opieters/MIRRA/3d_printing/radiation_shield/radiation_shield.scad

include <radiation_shield_optimised.scad>
include <radiation_shield_internal.scad>
include <hook.scad>

shield();
