opieters/MIRRA/firmware/sensor_node/sensornode.cpp

#include "sensornode.h"

#include <BatterySensor.h>
#include <ESPCamUART.h>
#include <LightSensor.h>
#include <RandomSensor.h>
#include <SoilTempSensor.h>
#include <TempHumiSensor.h>

RTC_DATA_ATTR bool initialBoot = true;

RTC_DATA_ATTR std::array<uint32_t, MAX_SENSORS> sensorsNextSampleTimes{0};
RTC_DATA_ATTR uint32_t sampleInterval{DEFAULT_SAMPLING_INTERVAL};
RTC_DATA_ATTR uint32_t sampleRounding{DEFAULT_SAMPLING_ROUNDING};
RTC_DATA_ATTR uint32_t sampleOffset{DEFAULT_SAMPLING_OFFSET};
RTC_DATA_ATTR uint32_t nextSampleTime = -1;
RTC_DATA_ATTR uint32_t commInterval;
RTC_DATA_ATTR uint32_t nextCommTime = -1;
RTC_DATA_ATTR uint32_t maxMessages;
RTC_DATA_ATTR MACAddress gatewayMAC;

SensorNode::SensorNode(const MIRRAPins& pins) : MIRRAModule(pins)
{
    if (initialBoot)
    {
        if (!LittleFS.exists(DATA_FP))
        {
            File dataFile{LittleFS.open(DATA_FP, FILE_WRITE, true)};
            dataFile.close();
        }
        initSensors();
        clearSensors();
        discovery();
        initialBoot = false;
    }
}

void SensorNode::wake()
{
    Log::debug("Running wake()...");
    uint32_t cTime{rtc.getSysTime()};
    if (cTime >= WAKE_COMM_PERIOD(nextCommTime))
        commPeriod();
    cTime = rtc.getSysTime();
    if (cTime >= nextSampleTime)
    {
        samplePeriod();
    }
    cTime = rtc.getSysTime();
    Log::info("Next sample in ", nextSampleTime - cTime, "s, next comm period in ", nextCommTime - cTime, "s");
    Serial.printf("Welcome! This is Sensor Node %s\n", lora.getMACAddress().toString());
    commandEntry.prompt(Commands(this));
    cTime = rtc.getSysTime();
    if (cTime >= nextCommTime || cTime >= nextSampleTime)
        wake();
    Log::debug("Entering deep sleep...");
    deepSleepUntil(std::min(WAKE_COMM_PERIOD(nextCommTime), nextSampleTime));
}

void SensorNode::discovery()
{
    Log::info("Awaiting discovery message...");
    auto hello = lora.receiveMessage<HELLO>(DISCOVERY_TIMEOUT);
    if (!hello)
    {
        Log::error("Error while awaiting discovery message from gateway. Aborting discovery listening.");
        return;
    }
    const MACAddress& gatewayMAC = hello->getSource();
    Log::info("Gateway found at ", gatewayMAC.toString(), ". Sending response message...");
    lora.sendMessage(Message<HELLO_REPLY>(lora.getMACAddress(), gatewayMAC));
    Log::debug("Awaiting time config message...");
    auto timeConfig = lora.receiveMessage<TIME_CONFIG>(TIME_CONFIG_TIMEOUT, TIME_CONFIG_ATTEMPTS, gatewayMAC);
    if (!timeConfig)
    {
        Log::error("Error while awaiting time config message from gateway. Aborting discovery listening.");
        return;
    }
    this->timeConfig(*timeConfig);
    Log::debug("Time config message received. Sending TIME_ACK");
    lora.sendMessage(Message<ACK_TIME>(lora.getMACAddress(), gatewayMAC));
    lora.receiveMessage<REPEAT>(TIME_CONFIG_TIMEOUT, 0, gatewayMAC);
}

void SensorNode::timeConfig(Message<TIME_CONFIG>& m)
{
    rtc.writeTime(m.getCTime());
    rtc.setSysTime();
    bool scheduleValid{sampleInterval == m.getSampleInterval() && sampleRounding == m.getSampleRounding() && sampleOffset == m.getSampleOffset()};
    sampleInterval = m.getSampleInterval() == 0 ? DEFAULT_SAMPLING_INTERVAL : m.getSampleInterval();
    sampleRounding = m.getSampleRounding() == 0 ? DEFAULT_SAMPLING_ROUNDING : m.getSampleRounding();
    sampleOffset = m.getSampleOffset();
    commInterval = m.getCommInterval();
    nextCommTime = m.getCommTime();
    maxMessages = m.getMaxMessages();
    gatewayMAC = m.getSource();
    if (!scheduleValid)
    {
        sensorsNextSampleTimes.fill(0);
        initSensors();
        clearSensors();
    }
    Log::info("Sample interval: ", sampleInterval, ", Comm interval: ", commInterval, ", Max messages: ", maxMessages,
              ", Gateway MAC: ", gatewayMAC.toString());
}

void SensorNode::addSensor(std::unique_ptr<Sensor>&& sensor)
{
    if (nSensors > MAX_SENSORS)
        return;
    uint32_t cTime{rtc.getSysTime()};
    if (sensorsNextSampleTimes[nSensors] == 0)
    {
        sensor->setNextSampleTime(((cTime / sampleRounding) * sampleRounding + sampleOffset));
        while (sensor->getNextSampleTime() <= cTime)
            sensor->updateNextSampleTime(sampleInterval);
    }
    else
    {
        sensor->setNextSampleTime(sensorsNextSampleTimes[nSensors]);
    }
    sensor->setup();
    sensors[nSensors] = std::move(sensor);
    nSensors++;
}

void SensorNode::initSensors()
{
    addSensor(std::make_unique<RandomSensor>(rtc.getSysTime()));
    addSensor(std::make_unique<SoilTemperatureSensor>(SOILTEMP_PIN, SOILTEMP_BUS_INDEX));
    addSensor(std::make_unique<LightSensor>());
    addSensor(std::make_unique<TempSHTSensor>());
    addSensor(std::make_unique<HumiSHTSensor>(*reinterpret_cast<TempSHTSensor*>(sensors[nSensors - 1].get())));
    addSensor(std::make_unique<BatterySensor>(BATT_PIN, BATT_EN_PIN));
    addSensor(std::make_unique<ESPCamUART>(&Serial1, CAM_PIN));
}

void SensorNode::clearSensors()
{
    nextSampleTime = -1;
    for (size_t i{0}; i < nSensors; i++)
    {
        sensorsNextSampleTimes[i] = sensors[i]->getNextSampleTime();
        if (sensors[i]->getNextSampleTime() < nextSampleTime)
            nextSampleTime = sensors[i]->getNextSampleTime();
        sensors[i].reset();
    }
    nSensors = 0;
}

Message<SENSOR_DATA> SensorNode::sampleAll()
{
    Log::info("Sampling all sensors...");
    for (size_t i{0}; i < nSensors; i++)
    {
        Serial.printf("Starting measurement for %u\n", sensors[i]->getID());
        sensors[i]->startMeasurement();
    }
    std::array<SensorValue, Message<SENSOR_DATA>::maxNValues> values;
    for (size_t i{0}; i < nSensors; i++)
    {
        Serial.printf("Getting measurement for %u\n", sensors[i]->getID());
        values[i] = sensors[i]->getMeasurement();
    }
    return Message<SENSOR_DATA>(lora.getMACAddress(), gatewayMAC, 0, static_cast<uint8_t>(nSensors), values);
}

Message<SENSOR_DATA> SensorNode::sampleScheduled(uint32_t cTime)
{
    Log::info("Sampling scheduled sensors...");
    for (size_t i{0}; i < nSensors; i++)
    {
        if (sensors[i]->getNextSampleTime() == cTime)
            sensors[i]->startMeasurement();
    }
    std::array<SensorValue, Message<SENSOR_DATA>::maxNValues> values;
    uint8_t nValues{0};
    for (size_t i{0}; i < nSensors; i++)
    {
        if (sensors[i]->getNextSampleTime() == cTime)
        {
            values[nValues] = sensors[i]->getMeasurement();
            nValues++;
        }
    }
    return Message<SENSOR_DATA>(lora.getMACAddress(), gatewayMAC, cTime, nValues, values);
}

void SensorNode::updateSensorsSampleTimes(uint32_t cTime)
{
    for (size_t i = 0; i < nSensors; i++)
    {
        while (sensors[i]->getNextSampleTime() <= cTime)
            sensors[i]->updateNextSampleTime(sampleInterval);
    }
}
void SensorNode::samplePeriod()
{
    initSensors();
    auto lambdaByNextSampleTime = [](const std::unique_ptr<Sensor>& a, const std::unique_ptr<Sensor>& b)
    { return a->getNextSampleTime() < b->getNextSampleTime(); };
    uint32_t cTime{(*std::min_element(sensors.begin(), std::next(sensors.begin(), nSensors), lambdaByNextSampleTime))->getNextSampleTime()};
    Message<SENSOR_DATA> message{sampleScheduled(cTime)};
    Log::debug("Constructed Sensor Message with length ", message.getLength());
    File data = LittleFS.open(DATA_FP, FILE_APPEND);
    storeSensorData(message, data);
    data.close();
    updateSensorsSampleTimes(cTime);
    clearSensors();
}

void SensorNode::commPeriod()
{
    uint32_t cTime{rtc.getSysTime()};
    if (cTime >= nextCommTime + (SENSOR_DATA_TIMEOUT / 1000))
    {
        Log::error("Too late to start comm period. Skipping and assuming next comm period from given interval.");
        while (nextCommTime <= cTime)
            nextCommTime += commInterval;
        return;
    }
    MACAddress _gatewayMAC{gatewayMAC}; // avoid access to slow RTC memory
    Log::info("Communicating with gateway ", _gatewayMAC.toString(), " ...");
    uint32_t _maxMessages{maxMessages}; // avoid access to slow RTC memory
    Log::debug("Max messages to send: ", _maxMessages);
    std::vector<Message<SENSOR_DATA>> messages;
    messages.reserve(_maxMessages);
    uint32_t messagesFlagPositions[_maxMessages];
    File dataFile = LittleFS.open(DATA_FP, "r+");
    while (dataFile.available())
    {
        if (messages.size() == _maxMessages)
            break;
        uint8_t size{static_cast<uint8_t>(dataFile.read())};
        uint8_t buffer[size];
        dataFile.read(buffer, size);
        if (buffer[0] == 0) // not yet uploaded
        {
            messagesFlagPositions[messages.size()] = dataFile.position() - size;
            Log::debug("Reconstructing message from buffer...");
            Message<SENSOR_DATA>& message{Message<SENSOR_DATA>::fromData(buffer)};
            message.setType(SENSOR_DATA);
            if ((messages.size() == _maxMessages - 1) ||
                (!dataFile.available())) // imperfect: assumes the last message in the data file is always one that has not been uploaded yet
            {
                Log::debug("Last sensor data message...");
                message.setLast();
            }
            messages.push_back(message);
        }
    }
    bool uploadSuccess[messages.size()];
    bool firstMessage{true};
    for (size_t i{0}; i < messages.size(); i++)
        uploadSuccess[i] = sendSensorMessage(messages[i], _gatewayMAC, firstMessage);
    for (size_t i{0}; i < messages.size(); i++)
    {
        if (uploadSuccess[i])
        {
            dataFile.seek(messagesFlagPositions[i]);
            dataFile.write(1);
        }
    }
    Log::debug("Messages that were uploaded have been marked as such.");
    dataFile.seek(0);
    pruneSensorData(std::move(dataFile), MAX_SENSORDATA_FILESIZE);
}

bool SensorNode::sendSensorMessage(Message<SENSOR_DATA>& message, MACAddress const& dest, bool& firstMessage)
{
    Log::debug("Sending data message...");
    if (firstMessage)
    {
        lightSleepUntil(nextCommTime);
        lora.sendMessage(message, 0); // gateway should already be listening for first message
        firstMessage = false;
    }
    else
    {
        lora.sendMessage(message);
    }
    Log::debug("Awaiting acknowledgement...");
    if (!message.isLast())
    {
        auto dataAck{lora.receiveMessage<ACK_DATA>(SENSOR_DATA_TIMEOUT, SENSOR_DATA_ATTEMPTS, dest)};
        if (dataAck)
        {
            return 1;
        }
        else
        {
            Log::error("Error while uploading to gateway.");
            return 0;
        }
    }
    else
    {
        auto timeConfig{lora.receiveMessage<TIME_CONFIG>(TIME_CONFIG_TIMEOUT, TIME_CONFIG_ATTEMPTS, dest)};
        if (timeConfig)
        {
            this->timeConfig(*timeConfig);
            lora.sendMessage(Message<ACK_TIME>(lora.getMACAddress(), dest));
            lora.receiveMessage<REPEAT>(TIME_CONFIG_TIMEOUT, 0, gatewayMAC);
            return 1;
        }
        else
        {
            Log::error("Error while receiving new time config from gateway. Assuming next comm period from given interval.");
            while (nextCommTime <= rtc.getSysTime())
                nextCommTime += commInterval;
            return 0;
        }
    }
}

CommandCode SensorNode::Commands::discovery()
{
    parent->discovery();
    return COMMAND_SUCCESS;
}
CommandCode SensorNode::Commands::sample()
{
    parent->samplePeriod();
    return COMMAND_SUCCESS;
}

CommandCode SensorNode::Commands::printSample()
{
    parent->initSensors();
    Message<SENSOR_DATA> message{parent->sampleAll()};
    auto& values = message.getValues();
    Serial.println("TAG\tVALUE");
    for (size_t i{0}, nValues{message.getNValues()}; i < nValues; i++)
    {
        Serial.printf("%u\t%f\n", values[i].tag, values[i].value);
    }
    parent->clearSensors();
    return COMMAND_SUCCESS;
}

CommandCode SensorNode::Commands::printSchedule()
{
    parent->initSensors();
    constexpr size_t timeLength{sizeof("0000-00-00 00:00:00")};
    char buffer[timeLength]{0};
    Serial.println("TAG\tNEXT SAMPLE");
    for (size_t i{0}; i < parent->nSensors; i++)
    {
        tm time;
        time_t nextSensorSampleTime{static_cast<time_t>(parent->sensors[i]->getNextSampleTime())};
        gmtime_r(&nextSensorSampleTime, &time);
        strftime(buffer, timeLength, "%F %T", &time);
        Serial.printf("%u\t%s\n", parent->sensors[i]->getID(), buffer);
    }
    parent->clearSensors();
    return COMMAND_SUCCESS;
}
